na103/rainbow100-memory/docs/Dec/PC100Bmem 01 P1100092.JPG

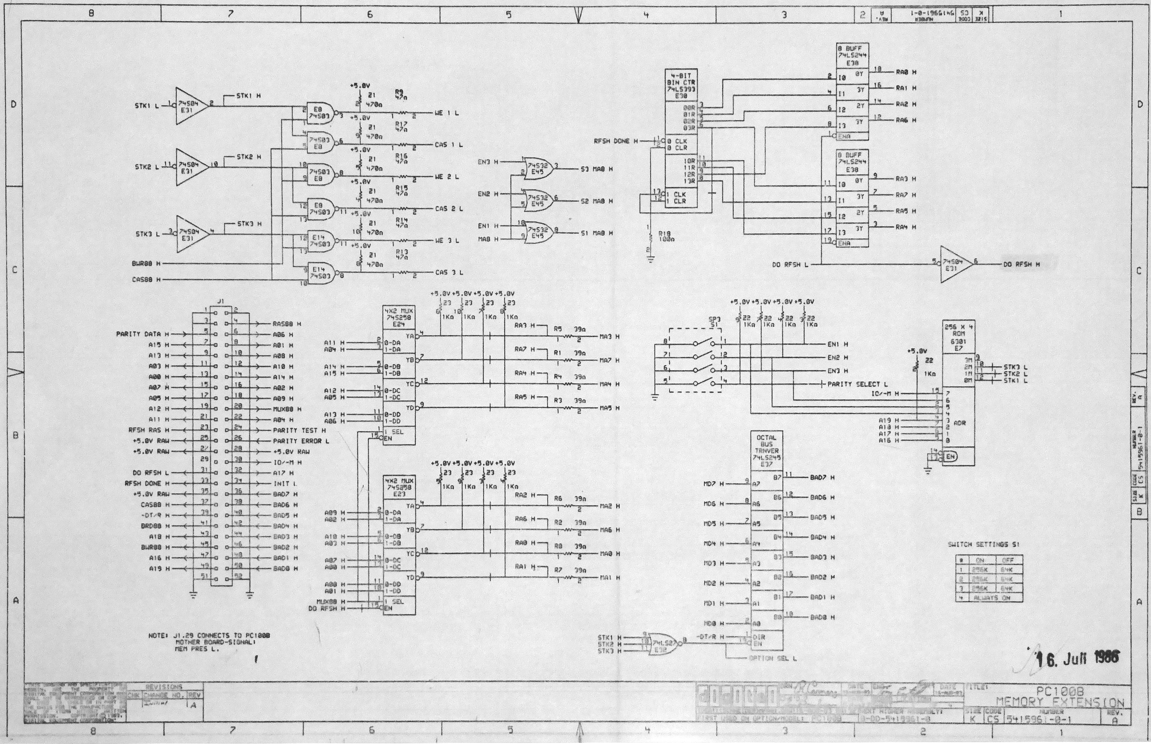
docs/Dec/PC100Bmem 01 P1100092.JPG
