na103/rainbow100-memory/docs/Dec/PC100Bmem 02 P1100094.JPG

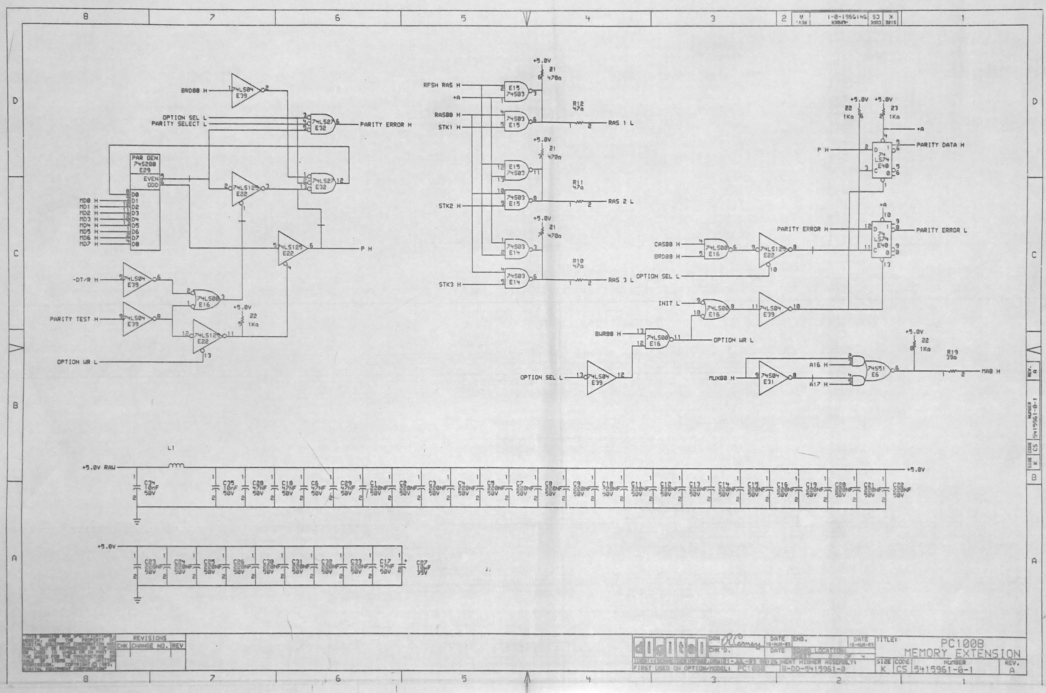
docs/Dec/PC100Bmem 02 P1100094.JPG
