na103/rainbow100-memory/docs/Dec/PC100Bmem 03 P1100096.JPG

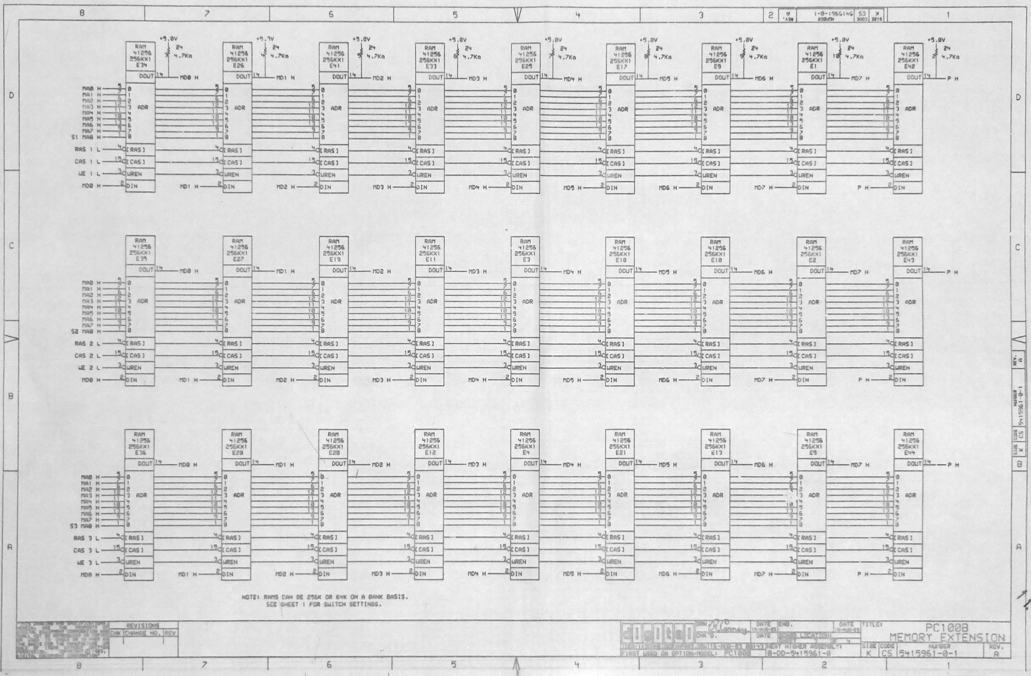
docs/Dec/PC100Bmem 03 P1100096.JPG
