na103/rainbow100-memory/docs/Dec/PC100Bmem 05 P1100101.JPG

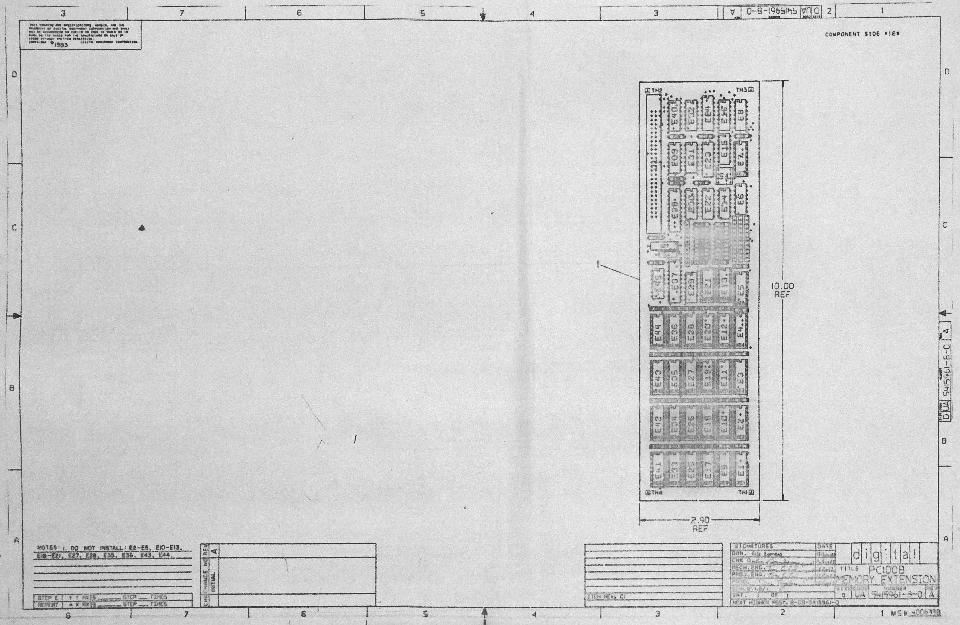
docs/Dec/PC100Bmem 05 P1100101.JPG
