na103/rainbow100-memory/docs/Dec/PC100Bmem 06 P1100104.JPG

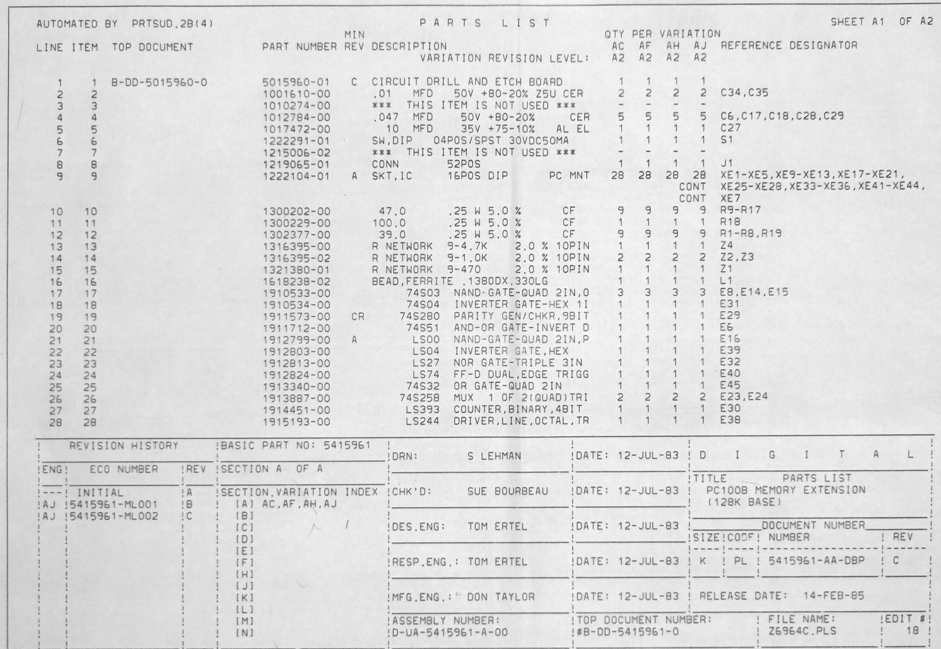
docs/Dec/PC100Bmem 06 P1100104.JPG
