na103/rainbow100-memory/docs/Dec/PC100Bmem 08 P1100107.JPG

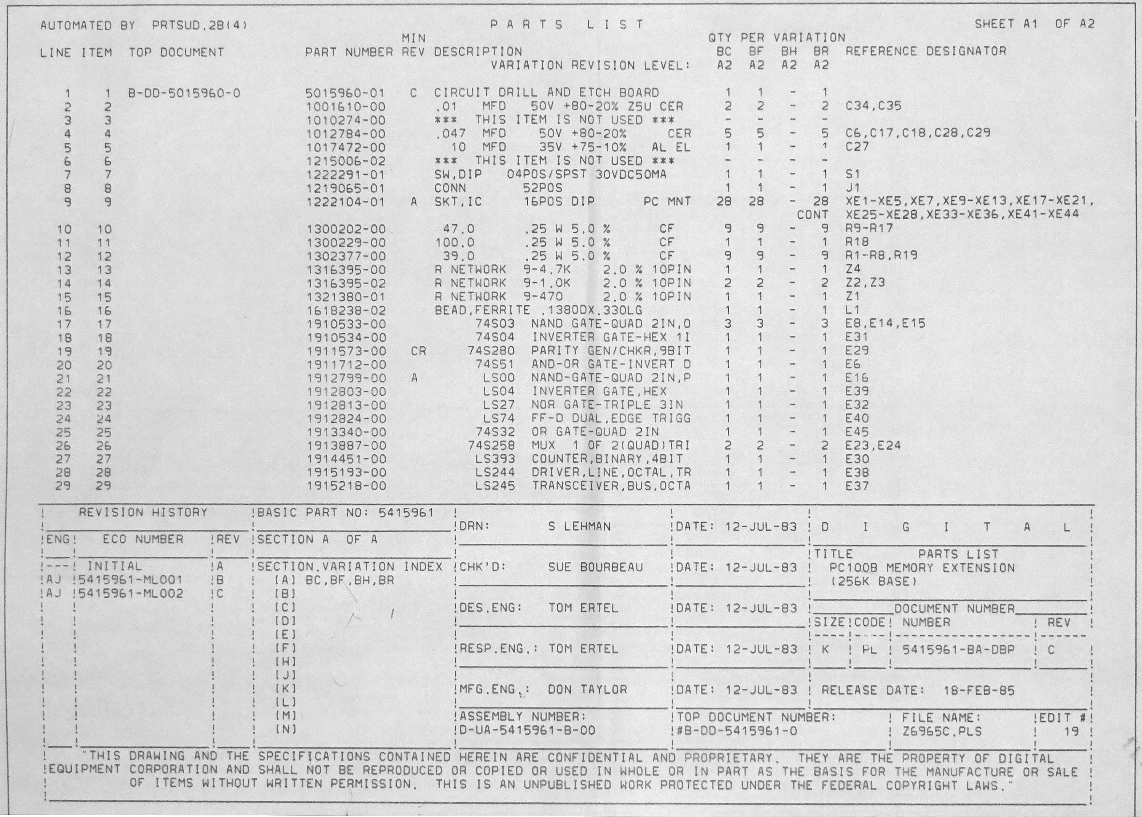
docs/Dec/PC100Bmem 08 P1100107.JPG
