na103/rainbow100-memory/img/DIP-768x472.png

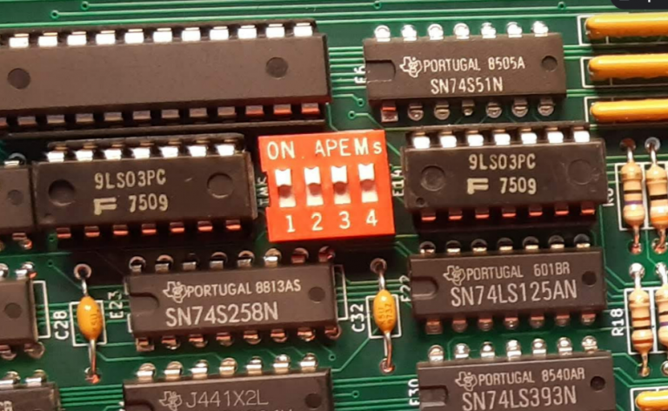
img/DIP-768x472.png
